mafiltenborg/supercharger/openscad/TI-59_LiPo_holder_PCB.scad

cube([49.7,9.8,0.8]);
